mrieker/pdp1134/ccode/z11dump.cc

//    Copyright (C) Mike Rieker, Beverly, MA USA
//    www.outerworldapps.com
//
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
//    EXPECT it to FAIL when someone's HeALTh or PROpeRTy is at RISk.
//
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
//    http://www.gnu.org/licenses/gpl-2.0.html

// Continuously dump the FPGA registers to the screen
// It does not write to the zynq memory pages so does not alter zynq state

//  ./z11dump.armv7l [-once] [-xmem <lo>..<hi>]...

#include <alloca.h>
#include <signal.h>
#include <stdint.h>
#include <stdio.h>
#include <stdlib.h>
#include <string.h>
#include <unistd.h>

#include "z11defs.h"
#include "z11util.h"

#define ESC_NORMV "\033[m"          // go back to normal video
#define ESC_REVER "\033[7m"         // turn reverse video on
#define ESC_UNDER "\033[4m"         // turn underlining on
#define ESC_BLINK "\033[5m"         // turn blink on
#define ESC_BOLDV "\033[1m"         // turn bold on
#define ESC_REDBG "\033[41m"        // red background
#define ESC_YELBG "\033[44m"        // yellow background
#define ESC_EREOL "\033[K"          // erase to end of line
#define ESC_EREOP "\033[J"          // erase to end of page
#define ESC_HOMEC "\033[H"          // home cursor

#define EOL ESC_EREOL "\n"
#define EOP ESC_EREOP

#define FIELD(index,mask) ((z11s[index] & mask) / (mask & - mask))

struct XMemRange {
    XMemRange *next;
    uint16_t loaddr;
    uint16_t hiaddr;
};

static char const *const fmstrs[] = { FMSTRS };

static bool volatile exitflag;
static char stdoutbuf[8000];

static void siginthand (int signum)
{
    exitflag = true;
}

int main (int argc, char **argv)
{
    setvbuf (stdout, stdoutbuf, _IOFBF, sizeof stdoutbuf);

    bool oncemode = false;
    bool pagemode = false;
    char const *eol = EOL;
    int fps = 20;
    XMemRange **lxmemrange, *xmemrange, *xmemranges;
    lxmemrange = &xmemranges;
    for (int i = 0; ++ i < argc;) {
        if (strcmp (argv[i], "-?") == 0) {
            puts ("");
            puts ("     Dump ZTurn FPGA state");
            puts ("     Does not alter the state");
            puts ("");
            puts ("  ./z11dump.armv7l [-fps <num> | -once | -page] [-xmem <lo>..<hi>]...");
            puts ("      -fps : this many frames per second 1..1000 (default 20)");
            puts ("     -once : just print the state once, else update continually");
            puts ("     -page : just dump the raw page then exit");
            puts ("     -xmem : dump the given extended memory range instead of register state");
            puts ("             may be given more than once");
            puts ("             Does not dump PDP-8/L core memory.  If need to dump low 4K memory,");
            puts ("             restart everything with z11real giving it the -enlo4k option.");
            puts ("");
            return 0;
        }
        if (strcasecmp (argv[i], "-fps") == 0) {
            if ((++ i >= argc) || (argv[i][0] == '-')) {
                fprintf (stderr, "missing <num> for -fps option\n");
                return 1;
            }
            char *p;
            fps = strtol (argv[i], &p, 0);
            if ((*p != 0) || (fps <= 0) || (fps > 1000)) {
                fprintf (stderr, "number frames per second %s must be integer 1..1000\n", argv[i]);
                return 1;
            }
            continue;
        }
        if (strcasecmp (argv[i], "-once") == 0) {
            eol = "\n";
            oncemode = true;
            continue;
        }
        if (strcasecmp (argv[i], "-page") == 0) {
            pagemode = true;
            continue;
        }
        if (strcasecmp (argv[i], "-xmem") == 0) {
            if ((++ i >= argc) || (argv[i][0] == '-')) {
                fprintf (stderr, "missing lo..hi address range after -xmem\n");
                return 1;
            }
            char *p;
            unsigned long hiaddr, loaddr;
            hiaddr = loaddr = strtoul (argv[i], &p, 8);
            if ((p[0] == '.') && (p[1] == '.')) {
                hiaddr = strtoul (p + 2, &p, 8);
            }
            if ((*p != 0) || (loaddr > hiaddr) || (hiaddr > 077777)) {
                fprintf (stderr, "bad address range %s must be <loaddr>..<hiaddr>\n", argv[i]);
                return 1;
            }
            xmemrange = (XMemRange *) alloca (sizeof *xmemrange);
            xmemrange->loaddr = loaddr;
            xmemrange->hiaddr = hiaddr;
            *lxmemrange = xmemrange;
            lxmemrange = &xmemrange->next;
            continue;
        }
        fprintf (stderr, "unknown argument %s\n", argv[i]);
        return 1;
    }
    *lxmemrange = NULL;

    Z11Page z11p;
    uint32_t volatile *pdpat = z11p.findev ("11", NULL, NULL, false);

    // maybe just dump the page and exit
    if (pagemode) {
        uint32_t words[1024];
        for (int i = 0; i < 1024; i ++) words[i] = ZRD(pdpat[i]);
        int k;
        for (k = 1024; words[--k] == 0xDEADBEEF;) { }
        for (int i = 0; i <= k; i += 8) {
            printf ("%03X:", i);
            for (int j = 0; j < 8; j ++) {
                printf (" %08X", words[i+j]);
            }
            printf ("\n");
        }
        return 0;
    }

#if 000
    uint32_t volatile *extmem = (xmemranges == NULL) ? NULL : z8p.extmem ();
#endif

    signal (SIGINT, siginthand);

    int pagelen = 1024;
    int itwirly = 4;
    while (! exitflag) {
        usleep (1000000 / fps);

        uint32_t z11s[1024];
        if (xmemranges == NULL) {
            for (int i = 0; i < pagelen; i ++) {
                z11s[i] = ZRD(pdpat[i]);
            }
        }

        if (! oncemode) printf (ESC_HOMEC);

        if (xmemranges == NULL) {
            uint32_t fpgamode = FIELD (Z_RA, a_fpgamode);
            uint32_t rsel1 = FIELD (Z_RC, c_rsel1_h);
            uint32_t rsel2 = FIELD (Z_RC, c_rsel2_h);
            uint32_t rsel3 = FIELD (Z_RC, c_rsel3_h);

            // zynq.v register dump
            printf ("VERSION=%08X 11  fpgamode=%o  FM_%s  debug=%08X  %c%s", z11s[0], fpgamode, fmstrs[fpgamode], z11s[8], "\\|/- "[itwirly], eol);
            printf ("      man_a_out_h=%06o  dmx_a_in_h=%06o     dev_a_h=%06o%s",           FIELD(Z_RB,b_man_a_out_h),      FIELD(Z_RF,f_dmx_a_in_h),      FIELD(Z_RD,d_dev_a_h),      eol);
            printf ("  man_ac_lo_out_h=%o       ac_lo_in_h=%o      dev_ac_lo_h=%o%s",       FIELD(Z_RA,a_man_ac_lo_out_h),  FIELD(Z_RC,c_ac_lo_in_h),      FIELD(Z_RD,d_dev_ac_lo_h),  eol);
            printf ("   man_bbsy_out_h=%o        bbsy_in_h=%o       dev_bbsy_h=%o%s",       FIELD(Z_RA,a_man_bbsy_out_h),   FIELD(Z_RC,c_bbsy_in_h),       FIELD(Z_RD,d_dev_bbsy_h),   eol);
            printf ("     man_bg_out_l=%02o         bg_in_l=%02o        dev_bg_l=%02o%s",   FIELD(Z_RB,b_man_bg_out_l),     FIELD(Z_RC,c_bg_in_l),         FIELD(Z_RE,e_dev_bg_l),     eol);
            printf ("     man_br_out_h=%02o     dmx_br_in_h=%02o        dev_br_h=%02o%s",   FIELD(Z_RB,b_man_br_out_h),     FIELD(Z_RE,e_dmx_br_in_h),     FIELD(Z_RE,e_dev_br_h),     eol);
            printf ("      man_c_out_h=%o       dmx_c_in_h=%o          dev_c_h=%o%s",       FIELD(Z_RB,b_man_c_out_h),      FIELD(Z_RE,e_dmx_c_in_h),      FIELD(Z_RE,e_dev_c_h),      eol);
            printf ("      man_d_out_h=%06o  dmx_d_in_h=%06o     dev_d_h=%06o%s",           FIELD(Z_RA,a_man_d_out_h),      FIELD(Z_RG,g_dmx_d_in_h),      FIELD(Z_RG,g_dev_d_h),      eol);
            printf ("  man_dc_lo_out_h=%o       dc_lo_in_h=%o      dev_dc_lo_h=%o%s",       FIELD(Z_RA,a_man_dc_lo_out_h),  FIELD(Z_RC,c_dc_lo_in_h),      FIELD(Z_RD,d_dev_dc_lo_h),  eol);
            printf ("                          hltgr_in_l=%o      dev_hltgr_l=%o%s",                                        FIELD(Z_RC,c_hltgr_in_l),      FIELD(Z_RD,d_dev_hltgr_l),  eol);
            printf ("  man_hltrq_out_h=%o   dmx_hltrq_in_h=%o      dev_hltrq_h=%o%s",       FIELD(Z_RA,a_man_hltrq_out_h),  FIELD(Z_RE,e_dmx_hltrq_in_h),  FIELD(Z_RD,d_dev_hltrq_h),  eol);
            printf ("   man_init_out_h=%o        init_in_h=%o       dev_init_h=%o%s",       FIELD(Z_RA,a_man_init_out_h),   FIELD(Z_RC,c_init_in_h),       FIELD(Z_RD,d_dev_init_h),   eol);
            printf ("   man_intr_out_h=%o        intr_in_h=%o       dev_intr_h=%o%s",       FIELD(Z_RA,a_man_intr_out_h),   FIELD(Z_RC,c_intr_in_h),       FIELD(Z_RD,d_dev_intr_h),   eol);
            printf ("   man_msyn_out_h=%o        msyn_in_h=%o       dev_msyn_h=%o      lataddr=%06o%s", FIELD(Z_RA,a_man_msyn_out_h), FIELD(Z_RC,c_msyn_in_h),   FIELD(Z_RD,d_dev_msyn_h), FIELD(Z_RK,k_lataddr), eol);
            printf ("    man_npg_out_l=%o         npg_in_l=%o        dev_npg_l=%o      latdata=%06o%s", FIELD(Z_RA,a_man_npg_out_l),  FIELD(Z_RC,c_npg_in_l),    FIELD(Z_RD,d_dev_npg_l),  FIELD(Z_RL,l_latdata), eol);
            printf ("    man_npr_out_h=%o     dmx_npr_in_h=%o        dev_npr_h=%o%s",       FIELD(Z_RA,a_man_npr_out_h),    FIELD(Z_RE,e_dmx_npr_in_h),    FIELD(Z_RD,d_dev_npr_h),    eol);
            printf ("     man_pa_out_h=%o      dmx_pa_in_h=%o         dev_pa_h=%o      turbo=%o%s",     FIELD(Z_RA,a_man_pa_out_h),   FIELD(Z_RE,e_dmx_pa_in_h), FIELD(Z_RD,d_dev_pa_h),   FIELD(Z_RL,l_turbo),   eol);
            printf ("     man_pb_out_h=%o      dmx_pb_in_h=%o         dev_pb_h=%o      simst=%02u%s",   FIELD(Z_RA,a_man_pb_out_h),   FIELD(Z_RE,e_dmx_pb_in_h), FIELD(Z_RD,d_dev_pb_h),   FIELD(Z_RK,k_simst),   eol);
            printf ("   man_sack_out_h=%o        sack_in_h=%o       dev_sack_h=%o      simpc=%06o%s",   FIELD(Z_RA,a_man_sack_out_h), FIELD(Z_RC,c_sack_in_h),   FIELD(Z_RD,d_dev_sack_h), FIELD(Z_RJ,j_simpc),   eol);
            printf ("   man_ssyn_out_h=%o        ssyn_in_h=%o       dev_ssyn_h=%o      simps=%06o%s",   FIELD(Z_RA,a_man_ssyn_out_h), FIELD(Z_RC,c_ssyn_in_h),   FIELD(Z_RD,d_dev_ssyn_h), FIELD(Z_RJ,j_simps),   eol);
            printf ("%s", eol);
            printf ("  man_rsel_h=%o   rsel1,2,3_h=%o,%o,%o   mux=%05o   cyc=%08X  armintena=%08X%s",  FIELD(Z_RB,b_man_rsel_h), rsel1, rsel2, rsel3, (z11s[Z_RC]>>17)&32767, z11s[9], z11s[ZG_INTENABS], eol);
            printf ("  ILA_ARMED=%o  ILA_AFTER=%05o  ILA_OFLOW=%o  ILA_INDEX=%05o   armintreq=%08X%s", FIELD(ILACTL,ILACTL_ARMED), FIELD(ILACTL,ILACTL_AFTER), FIELD(ILACTL,ILACTL_OFLOW), FIELD(ILACTL,ILACTL_INDEX), z11s[ZG_INTFLAGS], eol);

            for (int i = 0; i < pagelen;) {
                uint32_t idver = z11s[i];
                int j = i + (2 << ((idver >> 12) & 15));
                if (j > pagelen) {
                    pagelen = i;
                    break;
                }
                uint8_t idch1 = idver >> 24;
                uint8_t idch2 = idver >> 16;
                if ((idver & 0xF000U) == 0x0000U) {
                    printf ("%sVERSION=%08X %c%c %08X%s", eol, idver, idch1, idch2, z11s[i+1], eol);
                }
                if ((idver & 0xF000U) == 0x1000U) {
                    printf ("%sVERSION=%08X %c%c %08X %08X %08X%s", eol, idver, idch1, idch2, z11s[i+1], z11s[i+2], z11s[i+3], eol);
                }
                if ((idver & 0xF000U) == 0x2000U) {
                    printf ("%sVERSION=%08X %c%c %08X %08X %08X %08X %08X %08X %08X%s", eol, idver, idch1, idch2,
                        z11s[i+1], z11s[i+2], z11s[i+3], z11s[i+4], z11s[i+5], z11s[i+6], z11s[i+7], eol);
                }
                if ((idch1 == 'K') && (idch2 == 'Y')) {
                    printf ("                    haltreq=%o halted=%o stepreq=%u haltstate=%o haltins=%o%s",
                        FIELD(i+2,KY2_HALTREQ), FIELD(i+2,KY2_HALTED), FIELD(i+2,KY2_STEPREQ), FIELD(i+2,KY2_HALTSTATE), FIELD(i+2,KY2_HALTINS), eol);
                    printf ("                    dmastate=%o dmatimo=%o dmaperr=%o snapreq=%o snaphlt=%o%s",
                        FIELD(i+3,KY3_DMASTATE), FIELD(i+3,KY3_DMATIMO), FIELD(i+3,KY3_DMAPERR), FIELD(i+2,KY2_SNAPREQ), FIELD(i+2,KY2_SNAPHLT), eol);
                }
                if ((idver & 0xF000U) == 0x3000U) {
                    printf ("%sVERSION=%08X %c%c %08X %08X %08X %08X %08X %08X %08X%s", eol, idver, idch1, idch2,
                        z11s[i+1], z11s[i+2], z11s[i+3], z11s[i+4], z11s[i+5], z11s[i+6], z11s[i+7], eol);
                    printf ("           %08X %08X %08X %08X %08X %08X %08X %08X%s",
                        z11s[i+8], z11s[i+9], z11s[i+10], z11s[i+11], z11s[i+12], z11s[i+13], z11s[i+14], z11s[i+15], eol);
                }
                i = j;
            }
            itwirly = (itwirly + 1) & 3;
        } else {
#if 000
            // memory dump
            for (xmemrange = xmemranges; xmemrange != NULL; xmemrange = xmemrange->next) {
                uint16_t loaddr = xmemrange->loaddr;
                uint16_t hiaddr = xmemrange->hiaddr;
                fputs (eol, stdout);
                for (uint16_t lnaddr = loaddr & -16; lnaddr <= hiaddr; lnaddr += 16) {
                    printf (" %05o :", lnaddr);
                    for (uint16_t i = 0; i < 16; i ++) {
                        uint16_t addr = lnaddr + i;
                        if ((addr < loaddr) || (addr > hiaddr)) {
                            printf ("     ");
                        } else {
                            printf (" %04o", extmem[addr]);
                        }
                    }
                    fputs (eol, stdout);
                }
            }
#endif
        }

        if (oncemode) break;

        printf (EOP);
        fflush (stdout);
    }
    printf ("\n");
    return 0;
}
