mrieker/pdp1134/ccode/z11defs.h

//    Copyright (C) Mike Rieker, Beverly, MA USA
//    www.outerworldapps.com
//
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
//    EXPECT it to FAIL when someone's HeALTh or PROpeRTy is at RISk.
//
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
//    http://www.gnu.org/licenses/gpl-2.0.html

// bits provided by zynq.v in the zynq

#ifndef _Z11DEFS
#define _Z11DEFS

#include "km-zynqpdp11/zgintdefs.h"

#define Z_VER 0
#define Z_RA 1
#define Z_RB 2
#define Z_RC 3
#define Z_RD 4
#define Z_RE 5
#define Z_RF 6
#define Z_RG 7
#define Z_RJ 10
#define Z_RK 11
#define Z_RL 12

#define a_man_d_out_h     (0177777U << 0)
#define a_man_ssyn_out_h  (1U << 16)
#define a_man_sack_out_h  (1U << 17)
#define a_man_pb_out_h    (1U << 18)
#define a_man_pa_out_h    (1U << 19)
#define a_man_npr_out_h   (1U << 20)
#define a_man_npg_out_l   (1U << 21)
#define a_man_msyn_out_h  (1U << 22)
#define a_man_intr_out_h  (1U << 23)
#define a_man_init_out_h  (1U << 24)
#define a_man_hltrq_out_h (1U << 25)
#define a_man_dc_lo_out_h (1U << 26)
#define a_man_bbsy_out_h  (1U << 27)
#define a_man_ac_lo_out_h (1U << 28)
#define a_fpgamode    (3U << 30)

#define FM_OFF  0U    // reset FPGA and disconnect from bus
#define FM_SIM  1U    // simulated CPU, ignores PDP-11/34, disconnected from bus
#define FM_REAL 2U    // normal mode, assumes PDP-11/34 present
#define FM_MAN  3U    // manual control of all bus lines

#define FMSTRS "OFF", "SIM", "REAL", "MAN"

#define b_man_a_out_h  (0777777U << 0)
#define b_man_c_out_h  (3U << 18)
#define b_man_br_out_h (017U << 20)
#define b_man_bg_out_l (017U << 24)
#define b_man_rsel_h   (3U << 28)

#define c_muxa        (1U << 31)
#define c_muxb        (1U << 30)
#define c_muxc        (1U << 29)
#define c_muxd        (1U << 28)
#define c_muxe        (1U << 27)
#define c_muxf        (1U << 26)
#define c_muxh        (1U << 25)
#define c_muxj        (1U << 24)
#define c_muxk        (1U << 23)
#define c_muxl        (1U << 22)
#define c_muxm        (1U << 21)
#define c_muxn        (1U << 20)
#define c_muxp        (1U << 19)
#define c_muxr        (1U << 18)
#define c_muxs        (1U << 17)
#define c_rsel1_h     (1U << 16)
#define c_rsel2_h     (1U << 15)
#define c_rsel3_h     (1U << 14)
#define c_ac_lo_in_h  (1U << 13)
#define c_bbsy_in_h   (1U << 12)
#define c_dc_lo_in_h  (1U << 11)
#define c_hltgr_in_l  (1U << 10)
#define c_init_in_h   (1U <<  9)
#define c_intr_in_h   (1U <<  8)
#define c_msyn_in_h   (1U <<  7)
#define c_npg_in_l    (1U <<  6)
#define c_sack_in_h   (1U <<  5)
#define c_ssyn_in_h   (1U <<  4)
#define c_bg_in_l     (15U << 0)

#define d_dev_ac_lo_h (1U << 31)
#define d_dev_bbsy_h  (1U << 30)
#define d_dev_dc_lo_h (1U << 29)
#define d_dev_hltgr_l (1U << 28)
#define d_dev_hltrq_h (1U << 27)
#define d_dev_init_h  (1U << 26)
#define d_dev_intr_h  (1U << 25)
#define d_dev_msyn_h  (1U << 24)
#define d_dev_npg_l   (1U << 23)
#define d_dev_npr_h   (1U << 22)
#define d_dev_pa_h    (1U << 21)
#define d_dev_pb_h    (1U << 20)
#define d_dev_sack_h  (1U << 19)
#define d_dev_ssyn_h  (1U << 18)
#define d_dev_a_h     (0777777U << 0)

#define e_dmx_pb_in_h    (   1U << 27)
#define e_dmx_pa_in_h    (   1U << 26)
#define e_muxcount       (0377U << 18)
#define e_dmx_npr_in_h   (   1U << 17)
#define e_dmx_hltrq_in_h (   1U << 16)
#define e_dmx_c_in_h     (   3U << 14)
#define e_dev_c_h        (   3U << 12)
#define e_dmx_br_in_h    ( 017U <<  8)
#define e_dev_br_h       ( 017U <<  4)
#define e_dev_bg_l       ( 017U <<  0)

#define f_dmx_a_in_h  (0777777U <<  0)

#define g_dmx_d_in_h  (0177777U << 16)
#define g_dev_d_h     (0177777U <<  0)

#define j_simpc       (0x0000FFFFU)
#define j_simps       (0xFFFF0000U)
#define k_simst       (0x0000003FU)
#define k_lataddr     (0x00FFFFC0U)
#define l_muxdelay    (0x0000003FU)
#define l_latdata     (0x003FFFC0U)
#define l_turbo       (0x00400000U)
#define l_stepenable  (0x00800000U)
#define l_stepsingle  (0x01000000U)
#define l_stephalted  (0x80000000U)

#define ILACTL 034
#define ILATIM 035
#define ILADAT 036

#define ILACTL_DEPTH  8192
#define ILACTL_ARMED  0x80000000U
#define ILACTL_AFTER0 0x00010000U
#define ILACTL_OFLOW  0x00008000U
#define ILACTL_INDEX0 0x00000001U
#define ILACTL_AFTER  (ILACTL_AFTER0 * (ILACTL_DEPTH-1))
#define ILACTL_INDEX  (ILACTL_INDEX0 * (ILACTL_DEPTH-1))

#define BM_ENABLO     0xFFFFFFFFU
#define BM2_ENABHI    0x3FFFFFFFU
#define BM5_CTLREG    0xFFFF0000U
#define BM5_CTLENAB   0x00000010U
#define BM5_CTLADDR   0x0000000FU
#define BM6_BRJAME    0x00100000U
#define BM6_BRJAMA    0x000F0000U
#define BM6_BRENAB    0x0000FFFFU

#define KY_LIGHTS     0xFFFF0000U   // 777570 light register
#define KY_SWITCHES   0x0000FFFFU   // 777570 switch register

#define KY2_ENABLE    0x80000000U   // enable 777570 switches & lights registers
#define KY2_HALTREQ   0x40000000U   // request processor to halt
#define KY2_HALTED    0x20000000U   // processor has halted
#define KY2_STEPREQ   0x10000000U   // single-step processor
#define KY2_SNAPCTR   0x0F000000U   // snapshot counter
#define KY2_SR1716    0x00C00000U   // GUI SR<17:16> bits
#define KY2_HALTSTATE 0x00380000U
#define KY2_HLTRQOUTH 0x00040000U   // ky11.v is requesting processor to halt
#define KY2_HALTINS   0x00020000U   // processor has HALT instr in its IR
#define KY2_IRQLEV    0x0001C000U   // interrupt request level 4..7
#define KY2_IRQVEC    0x00003FC0U   // interrupt request vector[7:0]
#define KY2_SNAPBLK   0x00000004U   // block snapregs()
#define KY2_SNAPHLT   0x00000002U   // halt on completion of snapshot
#define KY2_SNAPREQ   0x00000001U   // initiate snapshot request

#define KY2_SNAPCTR0  (KY2_SNAPCTR & - KY2_SNAPCTR)

#define KY3_DMASTATE  0xE0000000U
#define KY3_DMATIMO   0x10000000U
#define KY3_DMACTRL   0x0C000000U
#define KY3_DMAPERR   0x02000000U
#define KY3_DMAADDR   0x0003FFFFU
#define KY4_SNAPREG   0xFFFF0000U
#define KY4_DMADATA   0x0000FFFFU
#define KY5_DMALOCK   0xFFFFFFFFU

#define KY3_DMASTATE0 (KY3_DMASTATE & - KY3_DMASTATE)
#define KY3_DMACTRL0  (KY3_DMACTRL  & - KY3_DMACTRL)
#define KY3_DMAADDR0  (KY3_DMAADDR  & - KY3_DMAADDR)
#define KY4_SNAPREG0  (KY4_SNAPREG  & - KY4_SNAPREG)
#define KY4_DMADATA0  (KY4_DMADATA  & - KY4_DMADATA)

#define RH1_MOLS 0xFF000000U
#define RH1_WRLS 0x00FF0000U
#define RH1_DTS  0x0000FF00U
#define RH1_VVS  0x000000FFU
#define RH2_WRT  0x80000000U
#define RH2_DRV  0x70000000U
#define RH2_CYL  0x0FFC0000U
#define RH2_ADR  0x0003FFFFU
#define RH3_PER  0x80000000U
#define RH3_NXM  0x40000000U
#define RH3_FER  0x20000000U
#define RH3_XGO  0x10000000U
#define RH3_WCE  0x08000000U
#define RH3_TRK  0x07C00000U
#define RH3_CLR  0x00200000U
#define RH3_SEC  0x001F0000U
#define RH3_WCT  0x0000FFFFU
#define RH4_ENAB 0x80000000U
#define RH4_FAST 0x40000000U
#define RH5_ATAS 0x000000FFU
#define RH5_DRYS 0x0000FF00U
#define RH5_RPCC 0x03FF0000U
#define RH5_ARMDS 0xE0000000U

#define RH1_MOLS0 (RH1_MOLS & - RH1_MOLS)
#define RH1_WRLS0 (RH1_WRLS & - RH1_WRLS)
#define RH1_DTS0  (RH1_DTS  & - RH1_DTS)
#define RH1_VVS0  (RH1_VVS  & - RH1_VVS)
#define RH2_DRV0  (RH2_DRV  & - RH2_DRV)
#define RH2_CYL0  (RH2_CYL  & - RH2_CYL)
#define RH2_ADR0  (RH2_ADR  & - RH2_ADR)
#define RH3_WCE0  (RH3_WCE  & - RH3_WCE)
#define RH3_TRK0  (RH3_TRK  & - RH3_TRK)
#define RH3_SEC0  (RH3_SEC  & - RH3_SEC)
#define RH3_WCT0  (RH3_WCT  & - RH3_WCT)
#define RH5_ATAS0 (RH5_ATAS & - RH5_ATAS)
#define RH5_DRYS0 (RH5_DRYS & - RH5_DRYS)
#define RH5_RPCC0 (RH5_RPCC & - RH5_RPCC)
#define RH5_ARMDS0 (RH5_ARMDS & - RH5_ARMDS)

#define RL1_RLCS  0x0000FFFFU
#define RL1_RLBA  0xFFFF0000U
#define RL2_RLDA  0x0000FFFFU
#define RL2_RLMP1 0xFFFF0000U
#define RL3_RLMP2 0x0000FFFFU
#define RL3_RLMP3 0xFFFF0000U
#define RL4_DRDY  0x0000000FU
#define RL4_DERR  0x000000F0U
#define RL4_DRONL 0x00000F00U
#define RL4_HDSEL 0x0000F000U
#define RL4_DTYPE 0x000F0000U
#define RL4_VOLCK 0x00F00000U
#define RL4_WRERR 0x0F000000U
#define RL4_WRLCK 0xF0000000U
#define RL4_DRDY0  (RL4_DRDY  & - RL4_DRDY)
#define RL4_DERR0  (RL4_DERR  & - RL4_DERR)
#define RL4_DRONL0 (RL4_DRONL & - RL4_DRONL)
#define RL4_HDSEL0 (RL4_HDSEL & - RL4_HDSEL)
#define RL4_DTYPE0 (RL4_DTYPE & - RL4_DTYPE)
#define RL4_VOLCK0 (RL4_VOLCK & - RL4_VOLCK)
#define RL4_WRERR0 (RL4_WRERR & - RL4_WRERR)
#define RL4_WRLCK0 (RL4_WRLCK & - RL4_WRLCK)
#define RL5_ENAB  0x80000000U
#define RL5_FAST  0x40000000U

#define TM2_MTBRC 0x0000FFFFU
#define TM2_MTCMA 0xFFFF0000U
#define TM4_FAST  0x40000000U
#define TM4_ENAB  0x80000000U

#define TM5_TURS  0x000000FFU
#define TM5_REWS  0x0000FF00U
#define TM5_WRLS  0x00FF0000U
#define TM5_BOTS  0xFF000000U
#define TM6_SELS  0x000000FFU

#define TM5_TURS0 (TM5_TURS & - TM5_TURS)
#define TM5_REWS0 (TM5_REWS & - TM5_REWS)
#define TM5_WRLS0 (TM5_WRLS & - TM5_WRLS)
#define TM5_BOTS0 (TM5_BOTS & - TM5_BOTS)
#define TM6_SELS0 (TM6_SELS & - TM6_SELS)

#define XE3_ENAB 0x80000000U

#endif
