mrieker/pdp1134/ccode/z11rl.cc

//    Copyright (C) Mike Rieker, Beverly, MA USA
//    www.outerworldapps.com
//
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
//    EXPECT it to FAIL when someone's HeALTh or PROpeRTy is at RISk.
//
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
//    http://www.gnu.org/licenses/gpl-2.0.html

// Performs RL01/RL02 disk I/O for the PDP-11 Zynq I/O board
// Runs as a background daemon when a file is loaded in a drive
// ...either with z11ctrl rlload command or GUI screen

//  ./z11rl [-reset]

// page references rl01/rl02 user guide sep 81

#include <errno.h>
#include <fcntl.h>
#include <pthread.h>
#include <stdint.h>
#include <stdio.h>
#include <stdlib.h>
#include <string.h>
#include <sys/stat.h>
#include <sys/time.h>
#include <unistd.h>

#include "futex.h"
#include "shmms.h"
#include "z11defs.h"
#include "z11util.h"

#define BLKNUM(da) ((uint16_t)((da >> 6) * 40 + (da & 63)))
#define SECCNT(wc) ((uint16_t)((65536 - wc + 127) / 128))

                        // (p25/v1-13)
#define NCYLS_RL01 256
#define NCYLS_RL02 512
#define NCYLS (dr->rl01?NCYLS_RL01:NCYLS_RL02)
#define SECPERTRK 40
#define TRKPERCYL 2
#define NSECS (NCYLS*TRKPERCYL*SECPERTRK)

#define WRDPERSEC 128

#define USPERCYL ((100000-15000)/(NCYLS-1))     // usec per cyl = (full seek - one seek) / (num cyls - 1)
#define SETTLEUS (15000-USPERCYL)               // settle time = one seek - usec per cyl
#define AVGROTUS 6500                           // average rotation usec
#define USPERWRD 4                              // usec per word
#define USPERSEC (AVGROTUS*2/SECPERTRK)         // usec per sector

#define NSPERDMA 2350
#define USLEEPOV 72

#define RFLD(n,m) ((ZRD(rlat[n]) & m) / (m & - m))

static char fns[4][SHMMS_FNSIZE];
static int debug;
static int fds[4];
static uint64_t seekdoneats[4];

#define LOCKIT shmms_svr_mutexlock(shmms)
#define UNLKIT shmms_svr_mutexunlk(shmms)

static ShmMS *shmms;
static uint32_t volatile *rlat;
static Z11Page *z11p;

static void *rliothread (void *dummy);
static uint64_t getnowus ();
static int setdrivetype (void *param, int drivesel);
static int fileloaded (void *param, int drivesel, int fd);
static int writebadblocks (ShmMSDrive *dr, int fd);
static void *timerthread (void *dsptr);
static void unloadfile (void *param, int drivesel);
static uint16_t headercrc (uint16_t accum, uint16_t dword);
static void dumpbuf (uint16_t drivesel, uint16_t const *buf, uint32_t off, uint32_t xba, char const *func);

int main (int argc, char **argv)
{
    memset (fds, -1, sizeof fds);

    bool resetit = (argc > 1) && (strcasecmp (argv[1], "-reset") == 0);

    // access fpga register set for the RL-11 controller
    // lock it so we are only process accessing it
    z11p = new Z11Page ();
    rlat = z11p->findev ("RL", NULL, NULL, true, false);

    // initialize shared memory - contains filenames and load/unload info
    shmms = shmms_svr_initialize (resetit, SHMMS_NAME_RL, "z11rl");
    shmms->ndrives = 4;

    // ...and no drives are ready or faulted
    ZWR(rlat[4], 0);
    UNLKIT;

    // enable board to process io instructions
    ZWR(rlat[5], (ZRD(rlat[5]) & RL5_FAST) | RL5_ENAB);

    debug = 0;
    char const *dbgenv = getenv ("z11rl_debug");
    if (dbgenv != NULL) debug = atoi (dbgenv);

    pthread_t rltid;
    int rc = pthread_create (&rltid, NULL, rliothread, NULL);
    if (rc != 0) ABORT ();
    for (int i = 0; i < 4; i ++) {
        rc = pthread_create (&rltid, NULL, timerthread, (void *)(long)i);
        if (rc != 0) ABORT ();
    }

    shmms_svr_proccmds (shmms, "z11rl", setdrivetype, fileloaded, unloadfile, NULL);

    return 0;
}

// get what sector is currently under the head
// - based on current time and rotation speed
#define SECUNDERHEAD (nowus / USPERSEC % SECPERTRK)

// do the disk file I/O
static void *rliothread (void *dummy)
{
    if (debug > 1) fprintf (stderr, "z11rl: thread started\n");

    int logrlfd = (debug < 0) ? open ("/tmp/logrl.bin", O_WRONLY | O_CREAT, 0666) : -1;

    while (true) {

        // wait for pdp to clear rlcs[07]
        z11p->waitint (ZGINT_RL);

        // block disk from being unloaded from under us
        LOCKIT;

        // see if command from pdp waiting to be processed
        uint16_t rlcs = RFLD (1, RL1_RLCS);
        if (! (rlcs & 0x0080)) {
            uint16_t rlba = RFLD (1, RL1_RLBA) & 0xFFFEU;
            uint16_t rlda = RFLD (2, RL2_RLDA);
            uint16_t rlmp = RFLD (2, RL2_RLMP1);
            uint16_t rlmp2, rlmp3, rdda;

            if (debug > 0) fprintf (stderr, "z11rl: start RLCS=%06o RLBA=%06o RLDA=%06o RLMP=%06o\n", rlcs, rlba, rlda, rlmp);

            uint32_t rlxba = ((rlcs & 0x30) << 12) + rlba;

            rlcs &= 0xC3FFU;                                            // clear error bits<13:10> in RLCS
                                                                        // rl11.v should have cleared them but do it here too

            bool fastio = (ZRD(rlat[5]) & RL5_FAST) != 0;               // skip any sleeping

            uint16_t drivesel = (rlcs >> 8) & 3;
            int fd = fds[drivesel];
            ZWR(rlat[4], ZRD(rlat[4]) & ~ (RL4_DRDY0 << drivesel));     // clear drive ready bit for selected drive while I/O in progress
            ShmMSDrive *dr = &shmms->drives[drivesel];

            uint64_t nowus = getnowus ();

            uint32_t seekdelay = (seekdoneats[drivesel] > nowus) ? seekdoneats[drivesel] - nowus : 0;
            uint32_t rotndelay = ((rlda & 63) + SECPERTRK - SECUNDERHEAD) % SECPERTRK;
            uint32_t xferdelay = (WRDPERSEC + 65535 - rlmp) / WRDPERSEC * USPERSEC - (NSPERDMA * (65536 - rlmp)) / 1000;
            uint32_t totldelay = seekdelay + rotndelay + xferdelay;
            totldelay = (totldelay > USLEEPOV) ? totldelay - USLEEPOV : 0;

            if (debug > 1) fprintf (stderr, "z11rl:       xba=%06o dsel=%u fd=%d\n", rlxba, drivesel, fd);

            switch ((rlcs >> 1) & 7) {

                // NOP - handled by fpga (rh11.v)
                case 0: ABORT ();

                // WRITE CHECK
                case 1: {
                    if (! fastio) usleep (totldelay);

                    if (debug > 0) fprintf (stderr, "z11rl: [%u]   writecheck wc=%06o da=%06o xba=%06o\n", drivesel, 65536 - rlmp, rlda, rlxba);

                    if (dr->curposn != (rlda & 0xFFC0U)) {
                        if (debug > 0) fprintf (stderr, "z11rl: [%u]       latestposition=%06o rlda=%06o\n", drivesel, dr->curposn, rlda);
                        goto hnferr;
                    }
                    uint16_t trk = (rlda >> 6) & 1;
                    uint16_t cyl =  rlda >> 7;

                    do {
                        uint16_t sec = rlda & 63;
                        if (sec >= SECPERTRK) {
                            if (debug > 0) fprintf (stderr, "z11rl: [%u]       sec=%02o\n", drivesel, sec);
                            goto hnferr;
                        }

                        uint16_t buf[WRDPERSEC];
                        uint32_t off = (((uint32_t) cyl * TRKPERCYL + trk) * SECPERTRK + sec) * sizeof buf;
                        int rc = pread (fd, buf, sizeof buf, off);
                        if (rc < 0) {
                            fprintf (stderr, "z11rl: [%u] error reading at %u: %m\n", drivesel, off);
                            goto opierr;
                        }
                        if (rc < (int) sizeof buf) {
                            fprintf (stderr, "z11rl: [%u] only read %d of %d bytes at %u\n", drivesel, rc, (int) sizeof buf, off);
                            goto opierr;
                        }
                        rlda ++;

                        z11p->dmalock ();
                        uint32_t rd = 0;
                        int i;
                        for (i = 0; i < WRDPERSEC; i ++) {
                            uint16_t memword;
                            rd = z11p->dmareadlocked (rlxba, &memword);
                            if (rd != 0) break;
                            if (memword != buf[i]) break;
                            rlxba = (rlxba + 2) & 0x3FFFE;
                            if (++ rlmp == 0) break;
                        }
                        z11p->dmaunlk ();
                        if (rd & KY3_DMATIMO) goto nxmerr;
                        if (rd & KY3_DMAPERR) goto mperr;
                        if (rd != 0) ABORT ();
                        if ((i < WRDPERSEC) && (rlmp != 0)) goto wckerr;
                    } while (rlmp != 0);
                    break;
                }

                // GET STATUS - handled by fpga (rh11.v)
                case 2: ABORT ();

                // SEEK
                // fpga (rl11.v) has already cleared drive ready (RLCS<00>)
                case 3: {
                    if (fd < 0) goto opierr;
                    if ((rlda & 0153) != 0001) goto opierr;

                    if (debug > 0) fprintf (stderr, "z11rl: [%u]   seek da=%06o\n", drivesel, rlda);

                    int32_t newcyl = dr->curposn >> 7;
                    if (rlda & 4) newcyl += rlda >> 7;
                             else newcyl -= rlda >> 7;
                    if (debug > 1) fprintf (stderr, "z11rl: [%u]       newcyl=%d\n", drivesel, newcyl);
                    if (newcyl < 0) newcyl = 0;
                    if (newcyl > NCYLS - 1) newcyl = (NCYLS - 1) & 07776;

                    uint32_t rl4 = ZRD(rlat[4]);
                    if (rlda & 16) rl4 |= RL4_HDSEL0 << drivesel;
                           else rl4 &= ~ (RL4_HDSEL0 << drivesel);
                    ZWR(rlat[4], rl4);

                    dr->curposn = (newcyl << 7) | ((rlda << 2) & 0x40);

                    if (! fastio) {
                        int oldsdaint = (int) seekdoneats[drivesel];
                        seekdoneats[drivesel] = nowus + (rlda >> 7) * USPERCYL + SETTLEUS;
                        if ((int) seekdoneats[drivesel] == oldsdaint) seekdoneats[drivesel] ++;
                        if (futex ((int *)&seekdoneats[drivesel], FUTEX_WAKE, 1000000000, NULL, NULL, 0) < 0) ABORT ();
                    }
                    break;
                }

                // READ HEADER
                case 4: {
                    if (debug > 0) fprintf (stderr, "z11rl: [%u]   readheader\n", drivesel);
                    totldelay = seekdelay + USPERSEC - nowus % USPERSEC;
                    if (! fastio) usleep (totldelay);   // wait for beginning of next sector
                    nowus += totldelay;
                    rlmp   = dr->curposn | SECUNDERHEAD;
                    rlmp2  = 0;
                    rlmp3  = headercrc (headercrc (0, rlmp), rlmp2);
                    goto rhddone;
                }

                // WRITE DATA
                case 5: {
                    if (! fastio) usleep (totldelay);

                    if (debug > 0) fprintf (stderr, "z11rl: [%u]   writedata wc=%06o da=%06o xba=%06o\n", drivesel, 65536 - rlmp, rlda, rlxba);

                    if (dr->curposn != (rlda & 0xFFC0U)) {
                        if (debug > 0) fprintf (stderr, "z11rl: [%u]       latestposition=%06o rlda=%06o\n", drivesel, dr->curposn, rlda);
                        goto hnferr;
                    }
                    uint16_t trk = (rlda >> 6) & 1;
                    uint16_t cyl =  rlda >> 7;

                    do {
                        uint16_t sec = rlda & 63;
                        if (sec >= SECPERTRK) {
                            if (debug > 0) fprintf (stderr, "z11rl: [%u]       sec=%02o\n", drivesel, sec);
                            goto hnferr;
                        }

                        z11p->dmalock ();
                        uint32_t xbasave = rlxba;
                        uint16_t buf[WRDPERSEC];
                        uint32_t rd = 0;
                        for (int i = 0; i < WRDPERSEC; i ++) {
                            rd = z11p->dmareadlocked (rlxba, &buf[i]);
                            if (rd != 0) break;
                            rlxba = (rlxba + 2) & 0x3FFFE;
                            if (++ rlmp == 0) {
                                memset (&buf[i+1], 0, (WRDPERSEC - i - 1) * sizeof buf[0]);
                                break;
                            }
                        }
                        z11p->dmaunlk ();
                        if (rd & KY3_DMATIMO) goto nxmerr;
                        if (rd & KY3_DMAPERR) goto mperr;
                        if (rd != 0) ABORT ();

                        uint32_t off = (((uint32_t) cyl * TRKPERCYL + trk) * SECPERTRK + sec) * sizeof buf;
                        int rc = pwrite (fd, buf, sizeof buf, off);
                        if (rc < 0) {
                            fprintf (stderr, "z11rl: [%u] error writing at %u: %m\n", drivesel, off);
                            goto opierr;
                        }
                        if (rc < (int) sizeof buf) {
                            fprintf (stderr, "z11rl: [%u] only wrote %d of %d bytes at %u\n", drivesel, rc, (int) sizeof buf, off);
                            goto opierr;
                        }
                        if (debug > 2) dumpbuf (drivesel, buf, off, xbasave, "write");

                        if (logrlfd >= 0) {
                            uint16_t hdr[] = { (uint16_t) (('W' << 8) + '0' + drivesel), rlda, (uint16_t) off, (uint16_t) (off >> 16) };
                            rc = write (logrlfd, hdr, sizeof hdr);
                            if (rc < (int) sizeof hdr) {
                                fprintf (stderr, "z11rl: [%u] only wrote %d of %d bytes to logrl\n", drivesel, rc, (int) sizeof hdr);
                                ABORT ();
                            }
                            rc = write (logrlfd, buf, sizeof buf);
                            if (rc < (int) sizeof buf) {
                                fprintf (stderr, "z11rl: [%u] only wrote %d of %d bytes to logrl\n", drivesel, rc, (int) sizeof buf);
                                ABORT ();
                            }
                        }

                        rlda ++;
                    } while (rlmp != 0);
                    break;
                }

                // READ DATA
                case 6: {
                    if (! fastio) usleep (totldelay);

                    if (debug > 0) fprintf (stderr, "z11rl: [%u]   readdata wc=%06o da=%06o xba=%06o\n", drivesel, 65536 - rlmp, rlda, rlxba);

                    if (dr->curposn != (rlda & 0xFFC0U)) {
                        if (debug > 0) fprintf (stderr, "z11rl: [%u]       latestposition=%06o rlda=%06o\n", drivesel, dr->curposn, rlda);
                        goto hnferr;
                    }
                    rdda = rlda;
                    goto readit;
                }

                // READ DATA WITHOUT HEADER CHECK
                case 7: {
                    if (debug > 0) fprintf (stderr, "z11rl: [%u]   readnohc wc=%06o da=%06o xba=%06o\n", drivesel, 65536 - rlmp, rlda, rlxba);

                    totldelay = seekdelay + USPERSEC - nowus % USPERSEC;
                    if (! fastio) usleep (totldelay);       // wait for beginning of next sector
                    nowus += totldelay;

                    rdda = dr->curposn | SECUNDERHEAD;      // disk address based on sector now under head
                    goto readit;
                }

                // read data with or without header check
                // - rdda = where we actually read from
                // - rlda = RLDA register contents
                readit: {
                    uint16_t trk = (rdda >> 6) & 1;
                    uint16_t cyl =  rdda >> 7;

                    do {
                        uint16_t sec = rdda & 63;
                        if (sec >= SECPERTRK) {
                            if (debug > 0) fprintf (stderr, "z11rl: [%u]       sec=%02o\n", drivesel, sec);
                            goto hnferr;
                        }

                        uint16_t buf[WRDPERSEC];
                        uint32_t off = (((uint32_t) cyl * TRKPERCYL + trk) * SECPERTRK + sec) * sizeof buf;
                        int rc = pread (fd, buf, sizeof buf, off);
                        if (rc < 0) {
                            fprintf (stderr, "z11rl: [%u] error reading at %u: %m\n", drivesel, off);
                            goto opierr;
                        }
                        if (rc < (int) sizeof buf) {
                            fprintf (stderr, "z11rl: [%u] only read %d of %d bytes at %u\n", drivesel, rc, (int) sizeof buf, off);
                            goto opierr;
                        }
                        if (debug > 2) dumpbuf (drivesel, buf, off, rlxba, "read");

                        if (logrlfd >= 0) {
                            uint16_t hdr[] = { (uint16_t) (('R' << 8) + '0' + drivesel), rdda, (uint16_t) off, (uint16_t) (off >> 16) };
                            rc = write (logrlfd, hdr, sizeof hdr);
                            if (rc < (int) sizeof hdr) {
                                fprintf (stderr, "z11rl: [%u] only wrote %d of %d bytes to logrl\n", drivesel, rc, (int) sizeof hdr);
                                ABORT ();
                            }
                            rc = write (logrlfd, buf, sizeof buf);
                            if (rc < (int) sizeof buf) {
                                fprintf (stderr, "z11rl: [%u] only wrote %d of %d bytes to logrl\n", drivesel, rc, (int) sizeof buf);
                                ABORT ();
                            }
                        }

                        rdda ++;
                        rlda ++;

                        z11p->dmalock ();
                        bool ok = true;
                        for (int i = 0; i < WRDPERSEC; i ++) {
                            ok = z11p->dmawritelocked (rlxba, buf[i]);
                            if (! ok) break;
                            rlxba = (rlxba + 2) & 0x3FFFE;
                            if (++ rlmp == 0) break;
                        }
                        z11p->dmaunlk ();
                        if (! ok) goto nxmerr;
                    } while (rlmp != 0);
                    break;
                }
            }
            goto alldone;
        opierr:;
            rlcs |= 1U << 10;                       // operation incomplete
            goto alldone;
        wckerr:;
            rlcs |= 2U << 10;                       // write check error
            goto alldone;
        hnferr:;
            if (! fastio) usleep (180000);          // ZRLHB0 wants a 160-400mS delay here
            rlcs |= 5U << 10;                       // header not found
            goto alldone;
        nxmerr:;
            rlcs |= 8U << 10;                       // non-existant memory
            goto alldone;
        mperr:;
            rlcs |= 9U << 10;                       // memory parity error
        alldone:;
            rlmp3 = rlmp2 = rlmp;
        rhddone:;

            // merge top bus address bits and set done bit
            rlcs  = (rlcs & ~ 0x30) | 0x80 | ((rlxba >> 12) & 0x30);

            // update drive ready before updating RLCS so rl11.v will fill in RLCS<00> correctly
            nowus = getnowus ();
            uint16_t drdy = ((fd >= 0) && (seekdoneats[drivesel] <= nowus)) ? RL4_DRDY0 : 0;
            ZWR(rlat[4], (ZRD(rlat[4]) & ~ (RL4_DRDY0 << drivesel)) | (drdy << drivesel));

            // update RLMPs, RLDA, then RLBA and RLCS
            ZWR(rlat[3], ((uint32_t) rlmp3 << 16) | rlmp2);
            ZWR(rlat[2], ((uint32_t) rlmp  << 16) | rlda);
            ZWR(rlat[1], ((uint32_t) rlxba << 16) | rlcs);
            if (debug > 0) fprintf (stderr, "z11rl: [%u]  done RLCS=%06o RLxBA=%06o RLDA=%06o RLMP=%06o %06o %06o\n",
                    drivesel, rlcs, rlxba, rlda, rlmp, rlmp2, rlmp3);
        }
        UNLKIT;
    }
}

// get current microsecond time
static uint64_t getnowus ()
{
    struct timespec nowts;
    if (clock_gettime (CLOCK_MONOTONIC, &nowts) < 0) ABORT ();
    return (nowts.tv_sec * 1000000ULL) + (nowts.tv_nsec / 1000);
}

// wait for changes in seekdoneats[drivesel]
// when time is up, set RL4_DRDY<drivesel> and clear seekdoneats[drivesel]
static void *timerthread (void *dsptr)
{
    int drivesel = (int)(long)dsptr;

    while (true) {

        // see if file open and seek in progress
        LOCKIT;
        struct timespec *tsptr = NULL;
        struct timespec timeout;
        uint64_t doneat = seekdoneats[drivesel];
        if ((fds[drivesel] >= 0) && (doneat != 0)) {
            struct timespec nowts;
            if (clock_gettime (CLOCK_MONOTONIC, &nowts) < 0) ABORT ();
            uint64_t nowus = (nowts.tv_sec * 1000000ULL) + (nowts.tv_nsec / 1000);

            // see if still waiting for seek to complete
            // if so, set up timeout for remaining delta
            if (doneat > nowus) {
                memset (&timeout, 0, sizeof timeout);
                timeout.tv_sec  = (doneat - nowus) / 1000000;
                timeout.tv_nsec = (doneat - nowus) % 1000000 * 1000;
                tsptr = &timeout;
            }

            // seek complete, mark drive ready
            // then leave tsptr NULL to wait indefinitely for next seek to begin
            else {
                ZWR(rlat[4], ZRD(rlat[4]) | (RL4_DRDY0 << drivesel));
                seekdoneats[drivesel] = doneat = 0;
            }
        }

        // wait for current seek complete or for another seek to be started
        UNLKIT;
        int rc = futex ((int *)&seekdoneats[drivesel], FUTEX_WAIT, (int)doneat, tsptr, NULL, 0);
        if ((rc < 0) && (errno != EAGAIN) && (errno != EINTR) && (errno != ETIMEDOUT)) ABORT ();
    }
}

static int setdrivetype (void *param, int drivesel)
{
    ShmMSDrive *dr = &shmms->drives[drivesel];
    char const *filenm = dr->filename;

    int fnlen = strlen (filenm);
         if ((fnlen >= 5) && (strcasecmp (filenm + fnlen - 5, ".rl01") == 0)) dr->rl01 = true;
    else if ((fnlen >= 5) && (strcasecmp (filenm + fnlen - 5, ".rl02") == 0)) dr->rl01 = false;
    else {
        fprintf (stderr, "z11rl: [%u] error decoding %s: name ends with neither .rl01 nor .rl02\n", drivesel, filenm);
        return -EBADF;
    }

    return 0;
}

// file was successfully opened
// save the fd and mark drive online
static int fileloaded (void *param, int drivesel, int fd)
{
    ShmMSDrive *dr = &shmms->drives[drivesel];
    if (! dr->readonly) {
        struct stat statbuf;
        if (fstat (fd, &statbuf) < 0) return -1;
        if (ftruncate (fd, NSECS * WRDPERSEC * 2) < 0) return -1;
        if (S_ISREG (statbuf.st_mode) && (statbuf.st_size == 0)) {
            if (writebadblocks (dr, fd) < 0) return -1;
        }
    }
    fds[drivesel] = fd;

    uint32_t rl4 = ZRD(rlat[4]);
    rl4 |=    RL4_DRDY0  << drivesel;                   // ready to accept a command
    rl4 &= ~ (RL4_DERR0  << drivesel);                  // no error state
    rl4 |=    RL4_DRONL0 << drivesel;                   // drive online
    if (dr->rl01) rl4 &= ~ (RL4_DTYPE0 << drivesel);    // drive is RL01
             else rl4 |=    RL4_DTYPE0 << drivesel;     // drive is RL02

    if (strcmp (fns[drivesel], dr->filename) != 0) {
        strcpy (fns[drivesel], dr->filename);
        rl4 |= RL4_VOLCK0 << drivesel;                  // volume check
        dr->curposn = 0;
    }

    rl4 &= ~ (RL4_WRERR0 << drivesel);                  // write error
    if (dr->readonly) rl4 |= RL4_WRLCK0 << drivesel;    // write locked
              else rl4 &= ~ (RL4_WRLCK0 << drivesel);   // write enabled
    ZWR(rlat[4], rl4);

    return 0;
}

// newly created file (it was empty)
// write a null badblock list so rsx is happy
// ref p1-9
static int writebadblocks (ShmMSDrive *dr, int fd)
{
    // get random bits for serial number
    uint16_t snbuf[2];
    int randfd = open ("/dev/urandom", O_RDONLY);
    if (randfd < 0) ABORT ();
    if (read (randfd, snbuf, sizeof snbuf) != (int) sizeof snbuf) ABORT ();
    close (randfd);

    // set up bad block file
    // written 4 sectors at a time
    uint16_t sectors0003[512];
    memset (sectors0003, -1, sizeof sectors0003);

    sectors0003[0] = snbuf[0] & 077777;
    sectors0003[1] = snbuf[1] & 077777;
    sectors0003[2] = 0;
    sectors0003[3] = 0;

    // fill last 40 sectors with repetition of those 4 sectors
    for (int i = NSECS - 40; i < NSECS; i += 4) {
        int rc = pwrite (fd, sectors0003, sizeof sectors0003, i * WRDPERSEC * 2);
        if (rc < 0) {
            fprintf (stderr, "z11rl: error writing badblock file at %u: %m\n",
                i * WRDPERSEC * 2);
            return -1;
        }
    }
    return 0;
}

// close file loaded on a disk drive
// mark drive offline
static void unloadfile (void *param, int drivesel)
{
    fns[drivesel][0] = 0;
    ZWR(rlat[4], ZRD(rlat[4]) & ~ ((RL4_DRDY0 | RL4_DRONL0) << drivesel));
    close (fds[drivesel]);
    fds[drivesel] = -1;
}

// accumulate header crc word
// - adapted from ZRLGC0 SIMBCC
static uint16_t headercrc (uint16_t accum, uint16_t dword)
{
    uint16_t const xpoly = 0120001;
    for (uint16_t temp2 = 16; temp2 > 0; -- temp2) {
        uint16_t bccfbk = ((dword ^ accum) & 1) ? xpoly : 0;
        dword >>= 1;
        accum >>= 1;
        accum ^= bccfbk;
    }
    return accum;
}

static void dumpbuf (uint16_t drivesel, uint16_t const *buf, uint32_t off, uint32_t xba, char const *func)
{
    fprintf (stderr, "  drv=%u off=%08o xba=%06o  %s\n", drivesel, off, xba, func);
    for (int i = 0; i < 128; i += 16) {
        fprintf (stderr, "   ");
        for (int j = 16; -- j >= 0;) {
            fprintf (stderr, " %06o", buf[i+j]);
        }
        fprintf (stderr, " : %03o\n", i);
    }
}
